damirzhamalatdinov/Velvet/Software/VelvetApp/Core/Inc/appInit.h

/* @file           : appInit.h
  * @date 23.02.2023  
  * @author Kamalov Marat  
  */
	
#ifndef __APPINIT_H
#define __APPINIT_H

#ifdef __cplusplus
extern "C" {
#endif

void initApp(void);

#ifdef __cplusplus
}
#endif

#endif /* __APPINIT_H */
