damirzhamalatdinov/Velvet/Software/VelvetApp/Core/Inc/uartCallback.h

/* @file           : uartCallback.h
  * @date 03.04.2023  
  * @author Kamalov Marat  
  */
	
#ifndef __UARTCALLBACK_H
#define __UARTCALLBACK_H

#ifdef __cplusplus
extern "C" {
#endif
#include <stdint.h>

void setReceiveStage (uint8_t stage);
#ifdef __cplusplus
}
#endif

#endif /* __UARTCALLBACK_H */
